Smit334/106A-DART/mcad/MotorGearDrive2.step

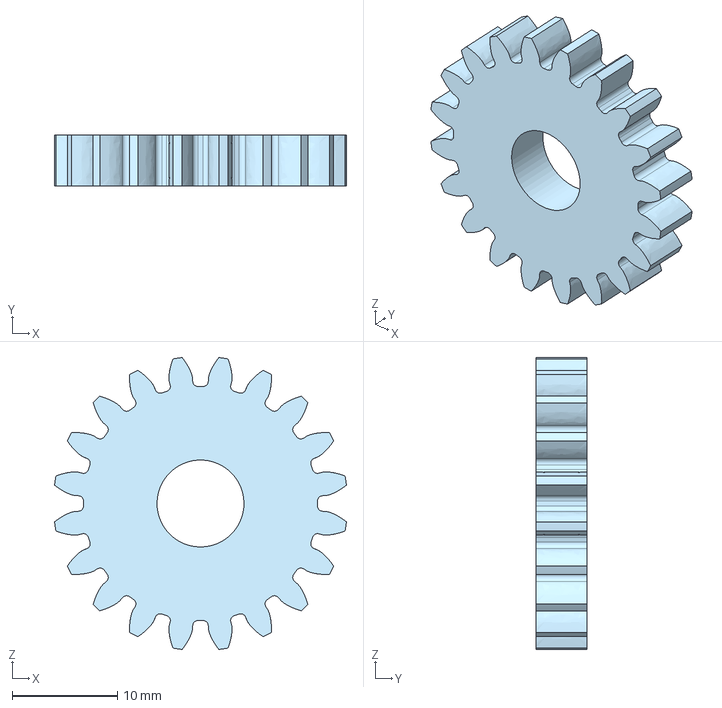
[picture p23: CAD file, 2024-12-20]
mcad/MotorGearDrive2.step
27.7 x 4.83 x 27.7 mm
