Smit334/106A-DART/mcad/refactored driving motor Copy 1.step

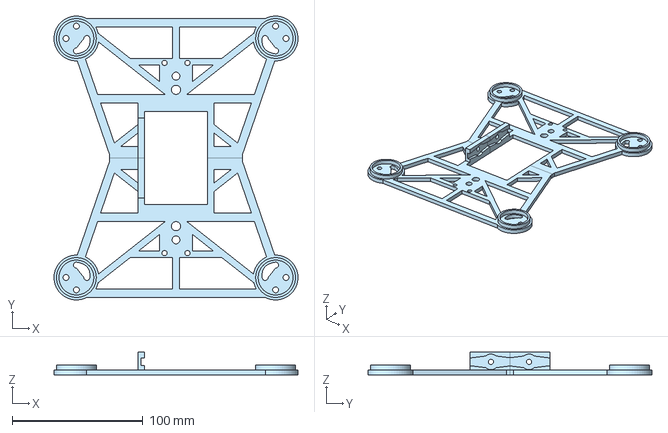
[picture p24: CAD file, 2024-12-20]
mcad/refactored driving motor Copy 1.step
186.7 x 217.2 x 17.5 mm
