Smit334/106A-DART/mcad/arm mockup.step

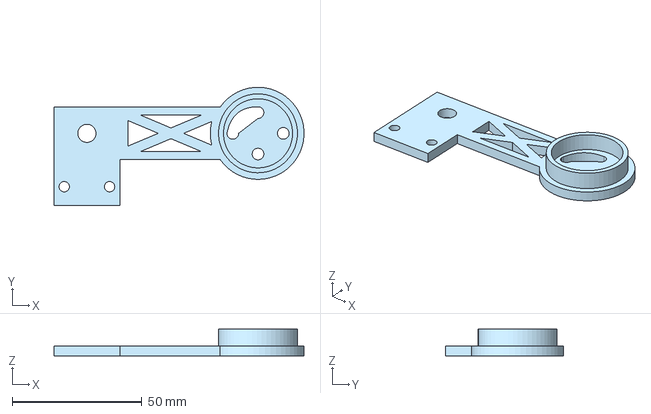
[picture p25: CAD file, 2024-12-20]
mcad/arm mockup.step
96.5 x 45.7 x 10.4 mm
