Smit334/106A-DART/mcad/Servo Motor Horn.step

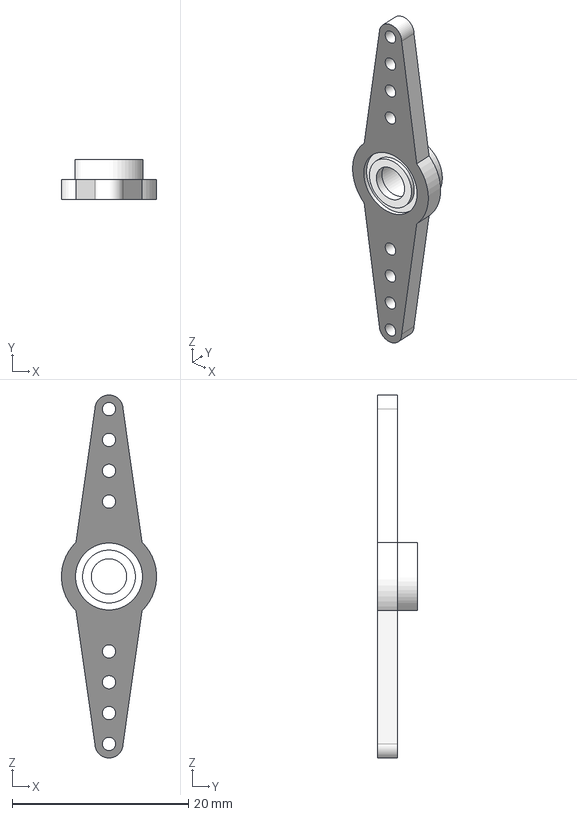
[picture p26: CAD file, 2024-12-20]
mcad/Servo Motor Horn.step
10.8 x 4.50 x 41.2 mm
