Smit334/106A-DART/mcad/driving gear (improved grip).step

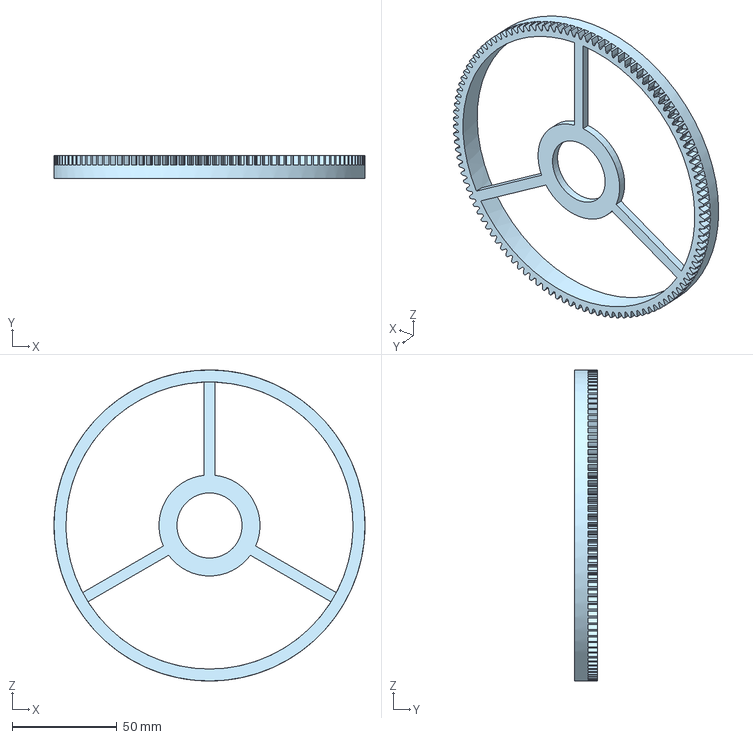
[picture p27: CAD file, 2024-12-20]
mcad/driving gear (improved grip).step
148.6 x 10.8 x 148.6 mm
