Smit334/106A-DART/mcad/Torodial Proppellor.step

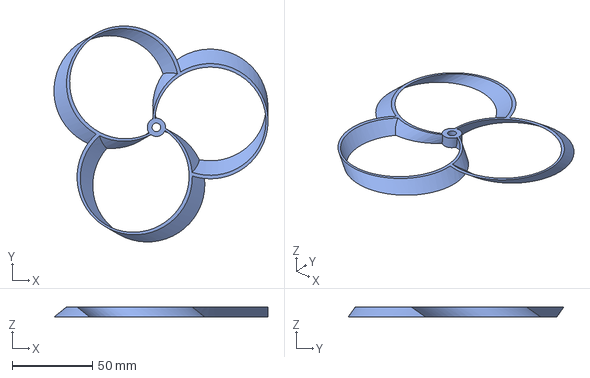
[picture p28: CAD file, 2024-12-20]
mcad/Torodial Proppellor.step
133.7 x 134.9 x 6.35 mm
