Smit334/106A-DART/mcad/tinyendcap.step

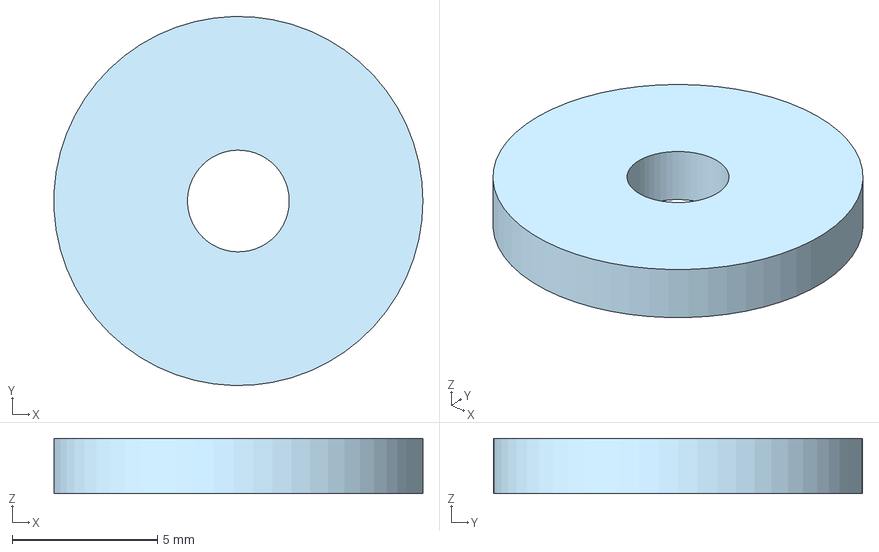
[picture p29: CAD file, 2024-12-20]
mcad/tinyendcap.step
12.7 x 12.7 x 1.91 mm
