Smit334/106A-DART/mcad/Wheel.step

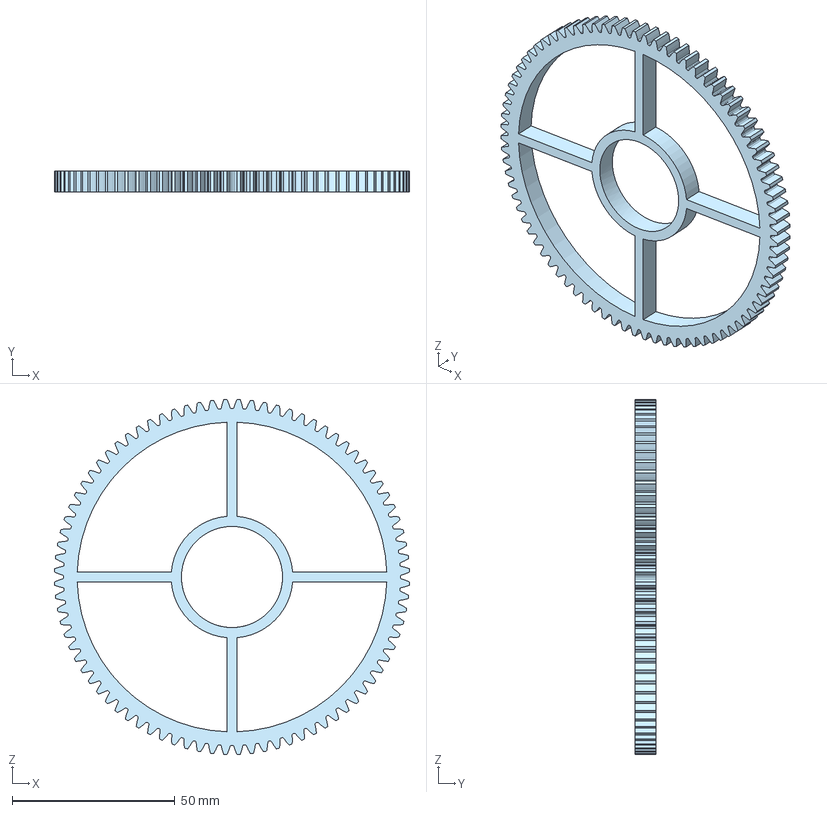
[picture p30: CAD file, 2024-12-20]
mcad/Wheel.step
109.2 x 6.35 x 109.2 mm
