Smit334/106A-DART/firmware/remote/common.h

#ifndef COMMON_H
#define COMMON_H

#pragma pack(1)

#include <stdint.h>

#define DRIVE_MODE 0
#define FLIGHT_MODE 1

#define RADIO_CH 130
#define RADIO_ADDR 0xE8E8F0F0E1LL

typedef uint8_t vehicle_mode_t;

typedef struct {
    uint16_t leftJoystickX:10;
    uint16_t leftJoystickY:10;
    uint8_t leftJoystickSelect:1;

    uint16_t rightJoystickX:10;
    uint16_t rightJoystickY:10;
    uint8_t rightJoystickSelect:1;

    vehicle_mode_t vehicleMode:1;
    uint8_t isAutoMode:1;
    uint8_t buttonOne:1;
    uint8_t buttonTwo:1;
    uint8_t buttonThree:1;
} RadioPacket;

#ifdef __cplusplus
inline void printPacket(RadioPacket *packet) {
  Serial.println("PACKET");

  Serial.print("Left Joystick X: ");
  Serial.println(packet->leftJoystickX);
  Serial.print("Left Joystick Y: ");
  Serial.println(packet->leftJoystickY);
  Serial.print("Left Joystick Select: ");
  Serial.println(packet->leftJoystickSelect);

  Serial.print("Right Joystick X: ");
  Serial.println(packet->rightJoystickX);
  Serial.print("Right Joystick Y: ");
  Serial.println(packet->rightJoystickY);
  Serial.print("Right Joystick Select: ");
  Serial.println(packet->rightJoystickSelect);

  Serial.print("Vehicle Mode: ");
  Serial.println(packet->vehicleMode);
  Serial.print("Auto Mode: ");
  Serial.println(packet->isAutoMode);
  Serial.print("Button One: ");
  Serial.println(packet->buttonOne);
  Serial.print("Button Two: ");
  Serial.println(packet->buttonTwo);
  Serial.print("Button Three: ");
  Serial.println(packet->buttonThree);
}
#endif

#endif
