Smit334/106A-DART/firmware/remote/util.h

#ifndef UTIL_H
#define UTIL_H

#include "common.h"

/* Radio pins */
#define RADIO_CE_PIN 10
#define RADIO_CSN_PIN 2
#define RADIO_IRQ_PIN 4

/* Joystick pins */
#define LEFT_JS_X_PIN A0
#define LEFT_JS_Y_PIN A1
#define LEFT_JS_SEL_PIN 0
#define RIGHT_JS_X_PIN A2
#define RIGHT_JS_Y_PIN A3
#define RIGHT_JS_SEL_PIN 1

/* Switch/button pins */
#define AUTO_MODE_SW_PIN 8
#define FLIGHT_MODE_SW_PIN 9
#define BTN_ONE_PIN 3
#define BTN_TWO_PIN 4
#define BTN_THREE_PIN 5 

#endif /* UTIL_H */
